JeffersonLab/daceri/sim/stl_exports/baseplate_robot-new.stl

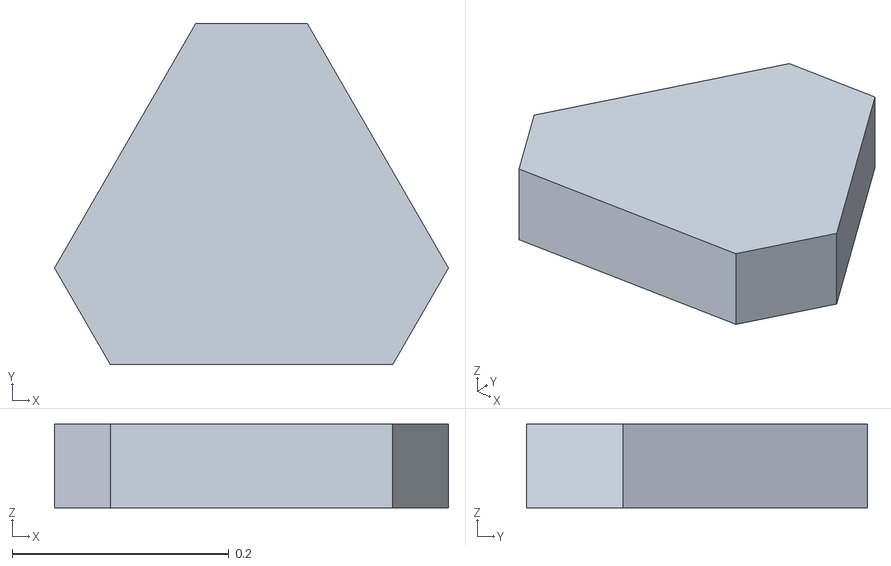
[picture p15: CAD file, 2024-12-02]
sim/stl_exports/baseplate_robot-new.stl
0.363 x 0.315 x 0.0772
