JeffersonLab/daceri/designs/Base/BatteryMountCase(Part2).STEP

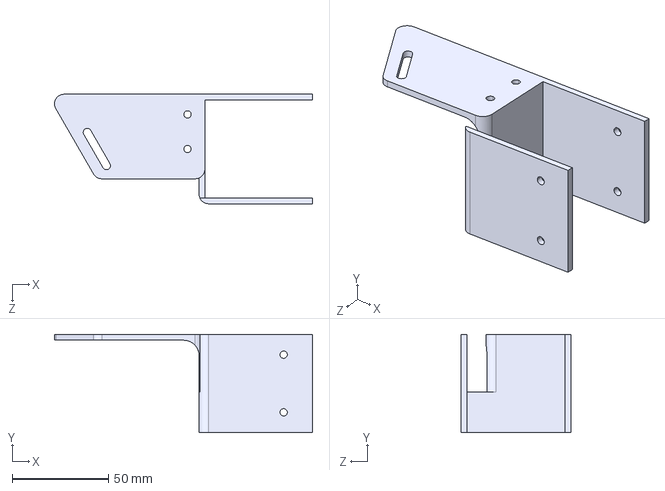
[picture p16: CAD file, 2025-07-11]
designs/Base/BatteryMountCase(Part2).STEP
134.2 x 51.0 x 57.0 mm
