JeffersonLab/daceri/designs/Elevator/sensor_holder_elev.obj

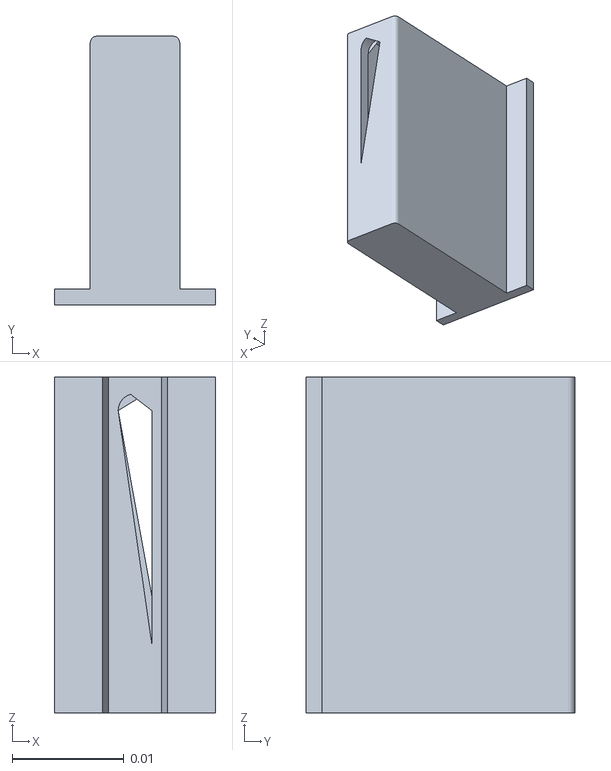
[picture p17: CAD file, 2025-02-25]
designs/Elevator/sensor_holder_elev.obj
0.0144 x 0.024 x 0.03
