JeffersonLab/daceri/sim/stl_exports/elevator-extended.stl

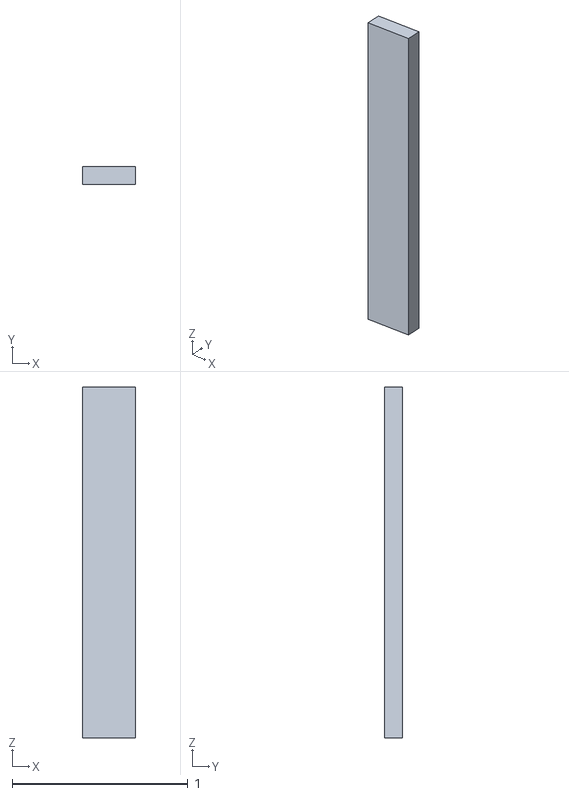
[picture p18: CAD file, 2024-10-11]
sim/stl_exports/elevator-extended.stl
0.3 x 0.1 x 2.00
