JeffersonLab/daceri/designs/Base/rev_control_hub_holder.obj

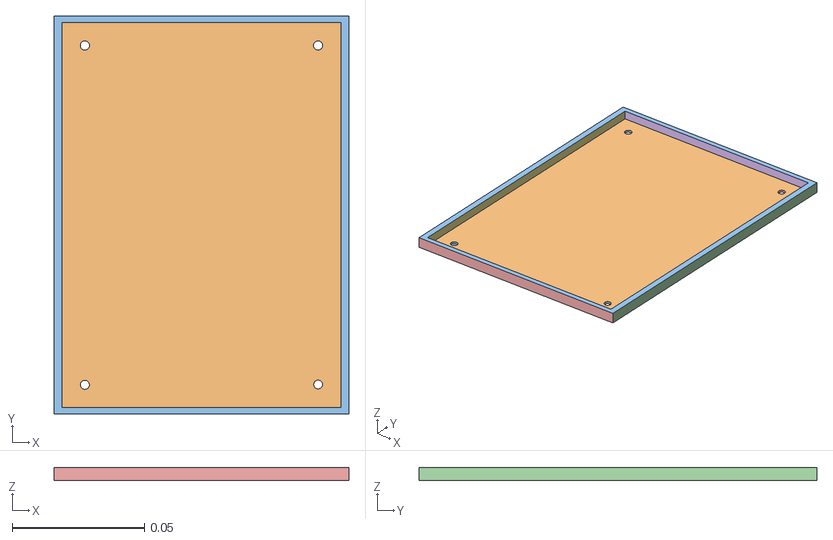
[picture p19: CAD file, 2025-07-11]
designs/Base/rev_control_hub_holder.obj
0.111 x 0.15 x 0.005
