JeffersonLab/daceri/sim/stl_exports/elevator-collapsed.stl

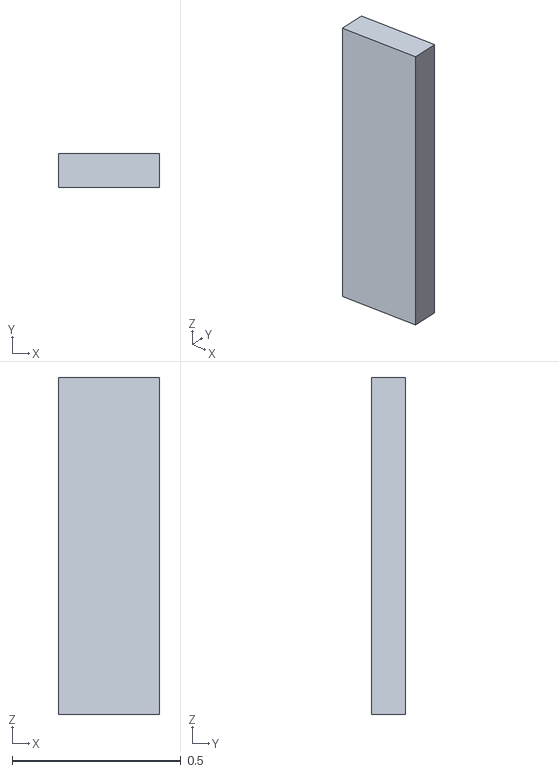
[picture p20: CAD file, 2024-10-11]
sim/stl_exports/elevator-collapsed.stl
0.3 x 0.1 x 1.00
