JeffersonLab/daceri/designs/Base/robot_base_elevator_holder.obj

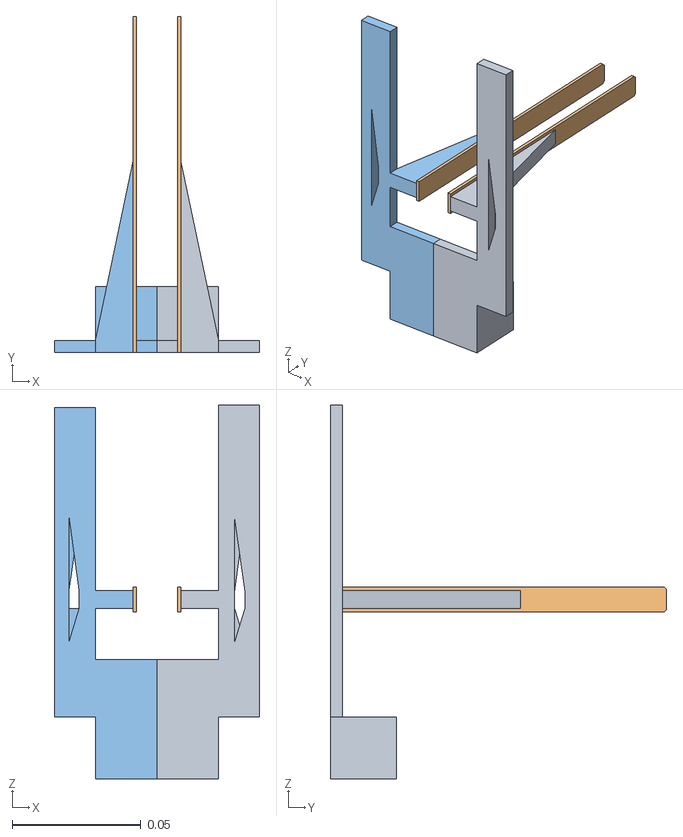
[picture p21: CAD file, 2025-02-25]
designs/Base/robot_base_elevator_holder.obj
0.0798 x 0.131 x 0.145
