JeffersonLab/daceri/designs/Base/robot_base.obj

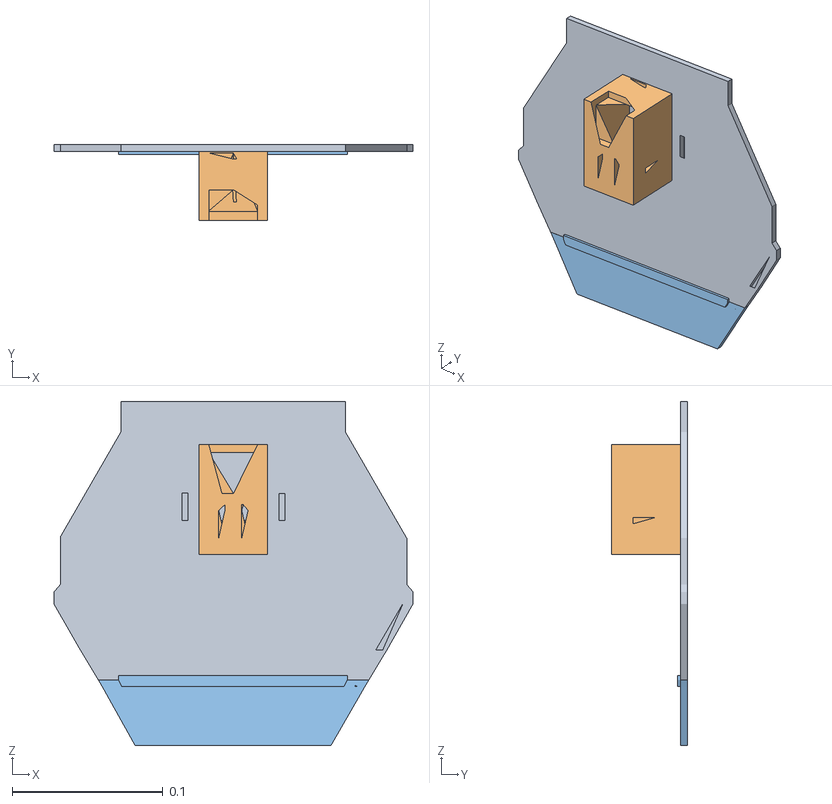
[picture p22: CAD file, 2025-02-25]
designs/Base/robot_base.obj
0.239 x 0.0505 x 0.229
Plane.001
Plane
