JeffersonLab/daceri/scripts/robot/bme280-script.py

# Script taken from: https://raw.githubusercontent.com/RuiSantosdotme/Random-Nerd-Tutorials/master/Projects/Raspberry-Pi/bme280_basic.py


import time
import smbus2
import bme280

# BME280 sensor address (default address)
address = 0x68

# Initialize I2C bus
bus = smbus2.SMBus(1)

# Load calibration parameters
calibration_params = bme280.load_calibration_params(bus, address)

def celsius_to_fahrenheit(celsius):
    return (celsius * 9/5) + 32

while True:
    try:
        # Read sensor data
        data = bme280.sample(bus, address, calibration_params)

        # Extract temperature, pressure, and humidity
        temperature_celsius = data.temperature
        pressure = data.pressure
        humidity = data.humidity

        # Convert temperature to Fahrenheit
        temperature_fahrenheit = celsius_to_fahrenheit(temperature_celsius)

        # Print the readings
        print("Temperature: {:.2f} °C, {:.2f} °F".format(temperature_celsius, temperature_fahrenheit))
        print("Pressure: {:.2f} hPa".format(pressure))
        print("Humidity: {:.2f} %".format(humidity))

        # Wait for a few seconds before the next reading
        time.sleep(2)

    except KeyboardInterrupt:
        print('Program stopped')
        break
    except Exception as e:
        print('An unexpected error occurred:', str(e))
        break
